sparkfun/Sound_Detector/documents/sims/sound_detector.asc

C3: cap; 10µ
D1: schottky; 1N5817
D2: schottky; 1N5817
R1: res; 22k
R2: res; 10k
R3: res; 1k
R4: res; 100
R5: res; 100
R6: res; 100k
R7: res; 3k3
R8: res; 100k
R13: res; 10k
R14: res; 100
U1: UniversalOpamp2
U2: UniversalOpamp2
U3: UniversalOpamp2
V1: voltage; 5
V2: voltage; SINE(0 2 100 .5 0 0 50)
Named nets: 0, vcc, envelope, gate
.tran 5
